Taro-Hayashi/KillerWhale/doc/leftside/4_TOP.md

# Killer Whale　TOP Unit LEFT Side Build Manual （[RIGHT Side](../rightside/4_TOP.md)）

1. [Start Page](../README_EN.md)
2. [BASE Unit](../leftside/2_BASE.md)
3. [SIDE Unit](../leftside/3_SIDE_TRACKBALL.md)
4. TOP Unit LEFT Side
   - [TOP Unit with wheel (sold separately)](../leftside/4_TOP_WHEEL.md)
5. [ADD Unit](../leftside/5_ADD.md)
6. [Assembly](../leftside/6_ASSEMBLE.md)
7. [Customizations](../leftside/7_CUSTOM.md)
8. [Misc](../leftside/8_MISC.md)
## Contents
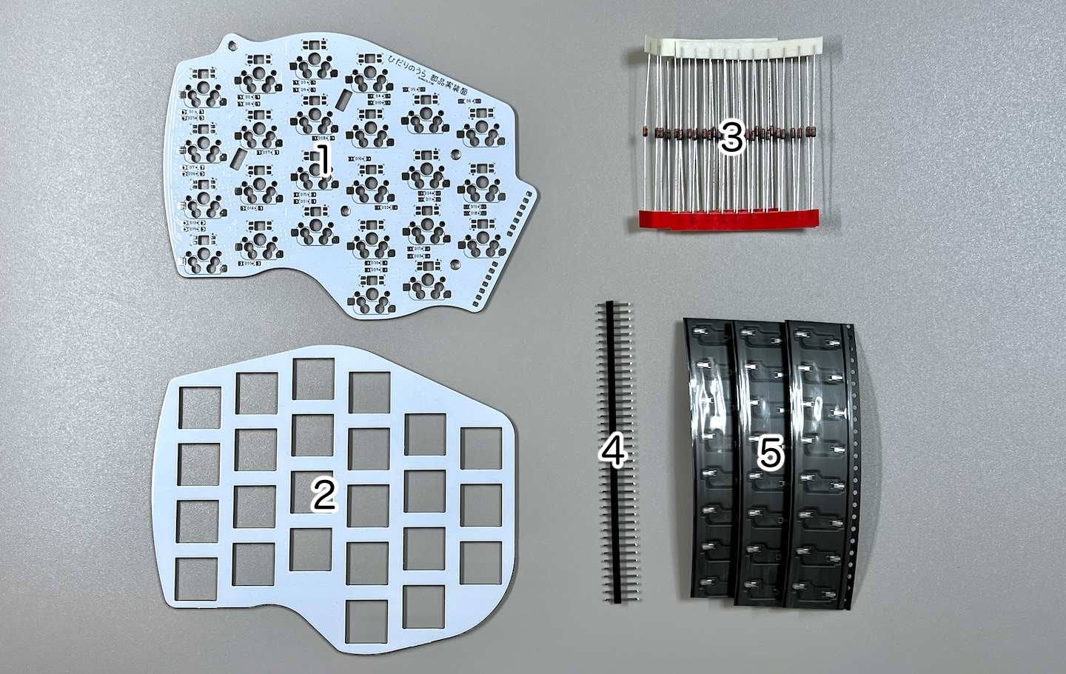
[picture p268: doc/img/4_1_top_l/4_1_1_contents.jpg]
  
||types|quantities||
|-|-|-|-|
|1|Main board|1|FR4|
|2|Switch plate|1|FR4|
|3|Diodes|30||
|4|Pin header|1||
|5|MX hotswap socket|24||

## Soldering

For the TOP unit, all components are soldered from the back side.
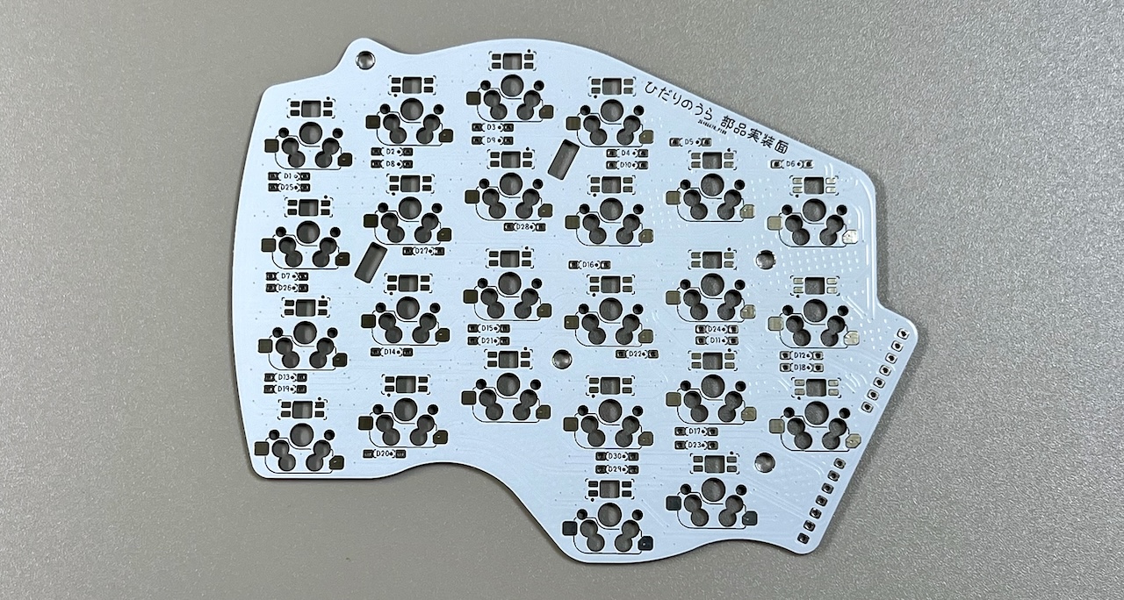
[picture p269: doc/img/4_1_top_l/4_1_2_overall.jpg]
  
### Soldering of the LEDs (optional)

> [!CAUTION]
> Orientation varies by location.

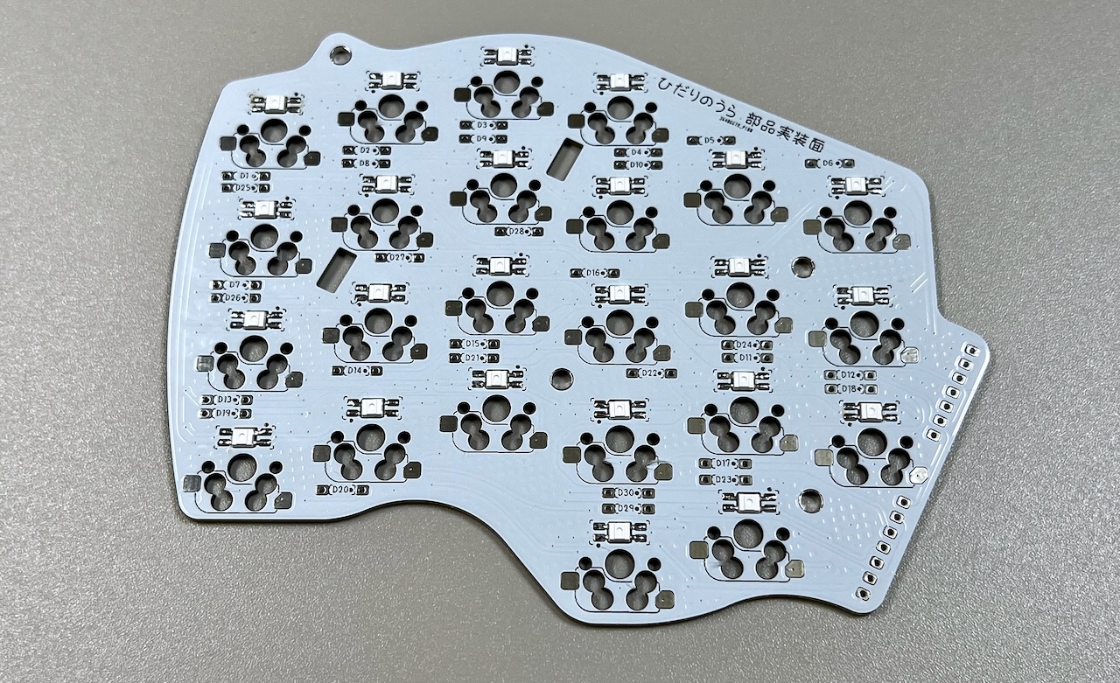
[picture p270: doc/img/4_1_top_l/4_1_3_led.jpg]
  

### Soldering of the diodes
Insert the diodes D1 to D30 from the bottom side of the PCB, and solder from the front side of the PCB and cut the diode legs.
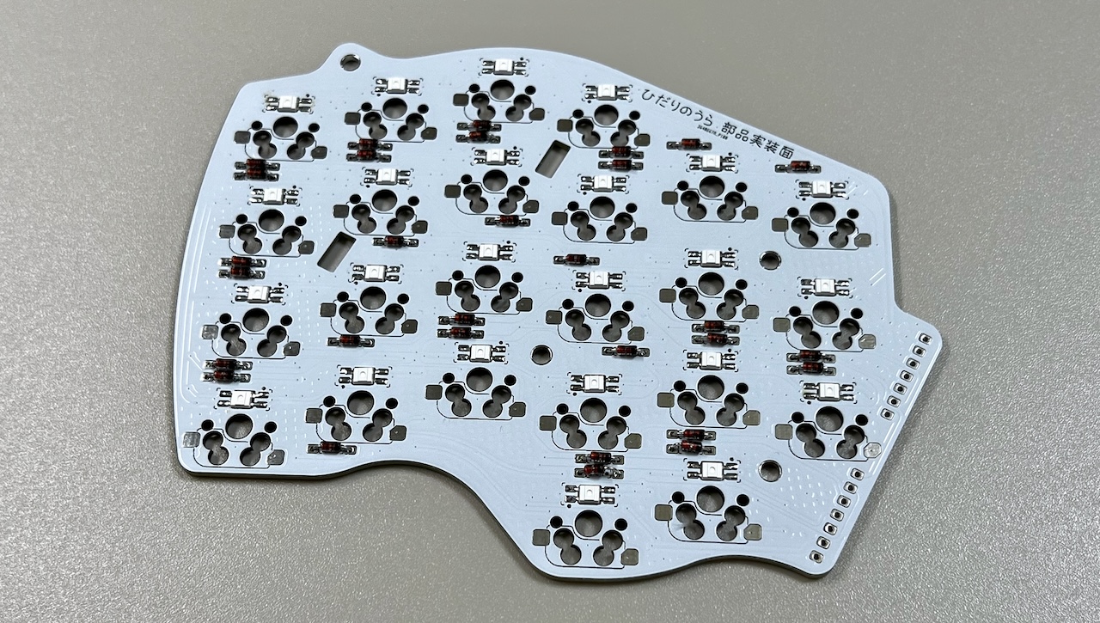
[picture p271: doc/img/4_1_top_l/4_1_4_diode.jpg]
 

### Soldering of the MX hotswap socket
Solder the MX hotswap sockets while keeping them in place with tweezers.
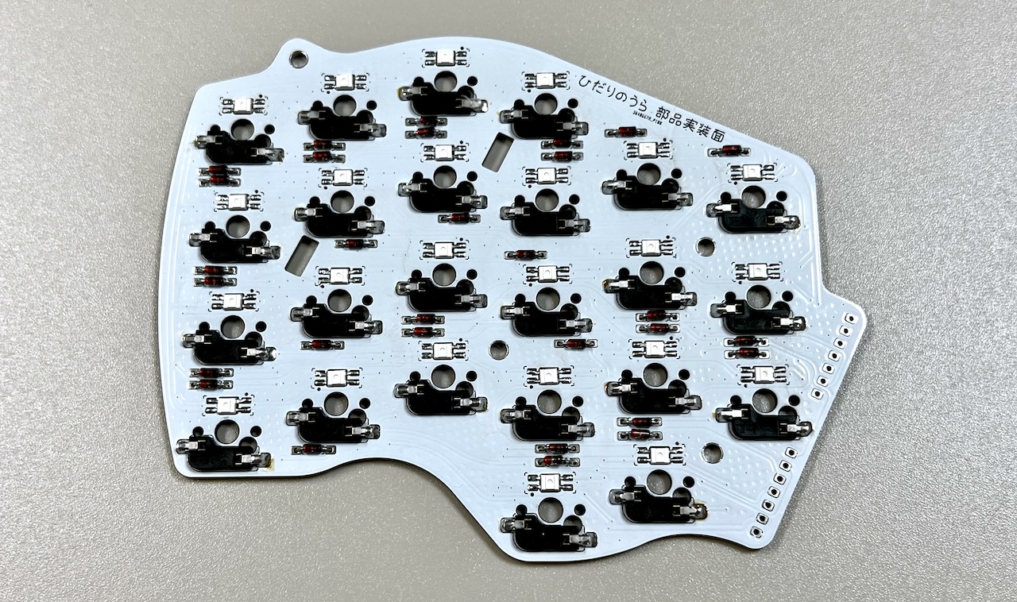
[picture p272: doc/img/4_1_top_l/4_1_5_mxsocket.jpg]
 

### Soldering od the pin headers
Cut out two sets of 7 pins from the 40 pin headers, insert from the back side of the PCB and solder. Insert the long side of the pins.
   
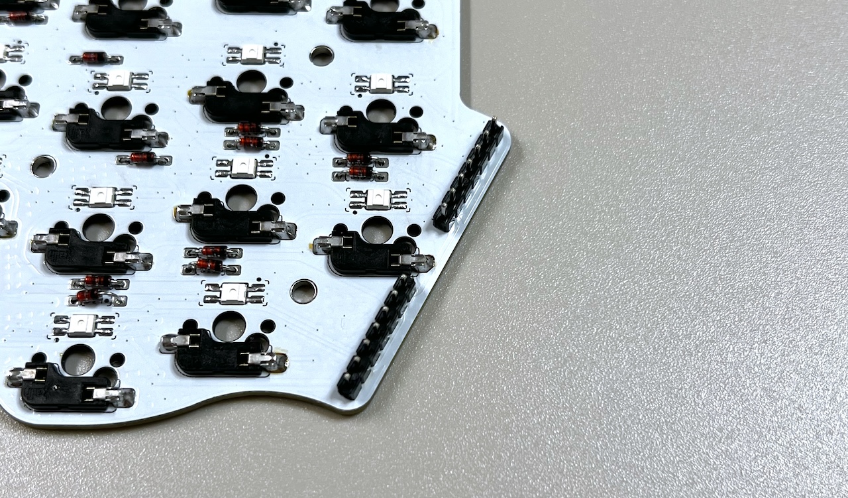
[picture p273: doc/img/4_1_top_l/4_1_6_pin_header.jpg]
 

## Intermediate assembly and soldering of sockets
If this is the first TOP unit that you have built, remove two sets of 7 pins from the remaining BASE unit pin headers, and insert them in the pin sockets of the TOP unit.

   
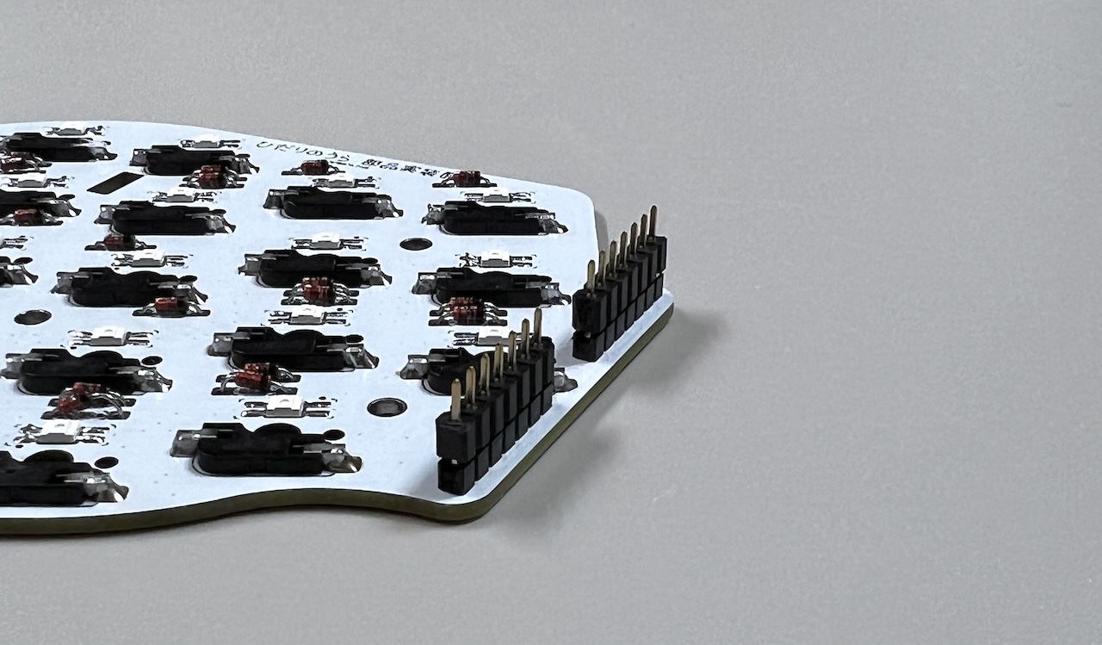
[picture p274: doc/img/4_1_top_l/4_1_7_pin_socket.jpg]
 
Place the TOP unit on the supports and secure it with the M3 screws excessed in base unit.
> [!NOTE]
>  Make sure that the legs of the pin sockets are inside the long through-holes of the base unit.

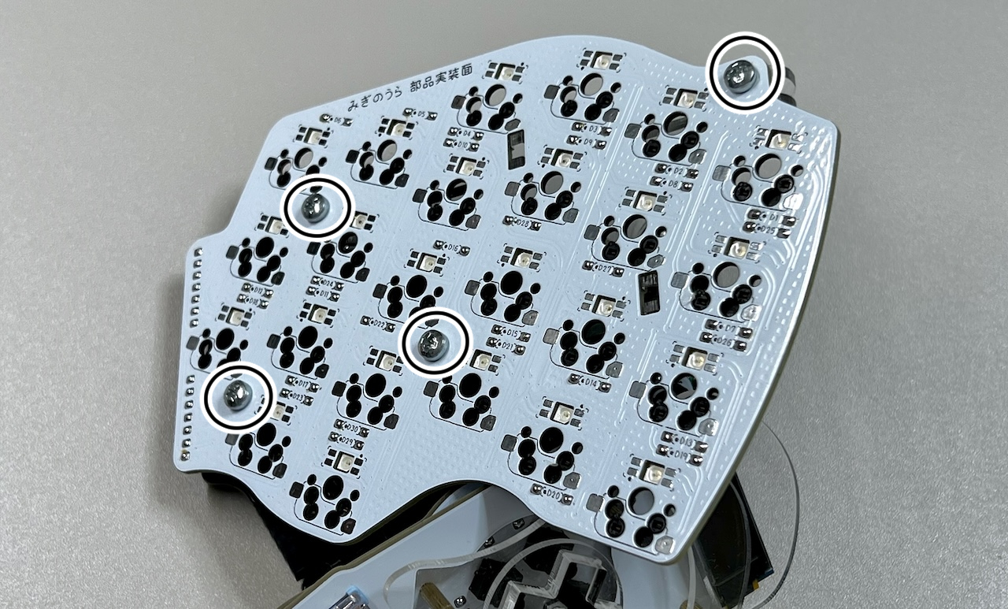
[picture p275: doc/img/4_1_top_l/4_1_8_base_1.jpg]
 
Solder the pin sockets from the back side of the base unit.
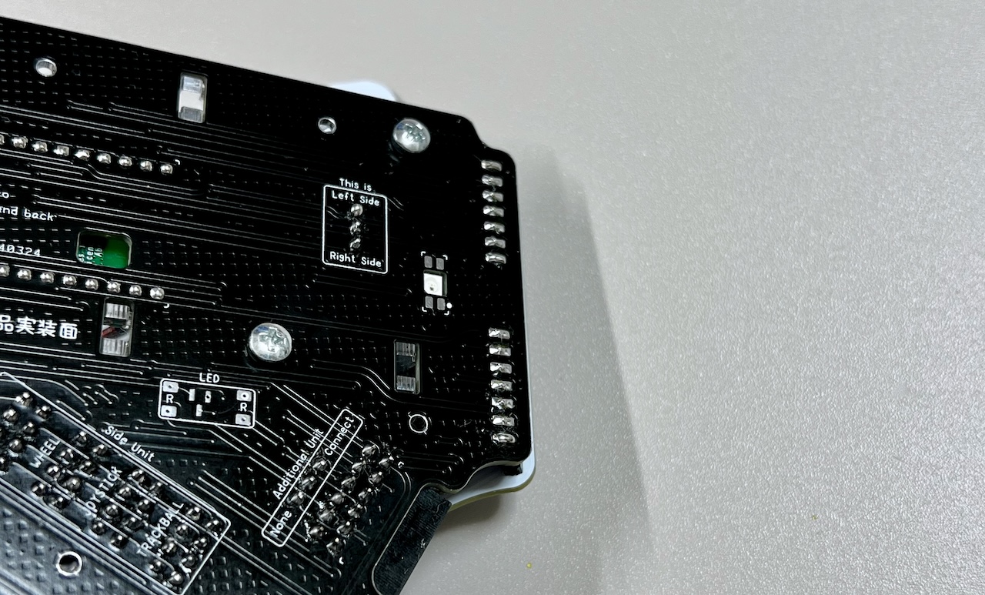
[picture p276: doc/img/4_1_top_l/4_1_9_base_2.jpg]
 
Switch plate and all switches are in place, then confirm that everything is working by connecting the unit to a computer with a USB cable. 
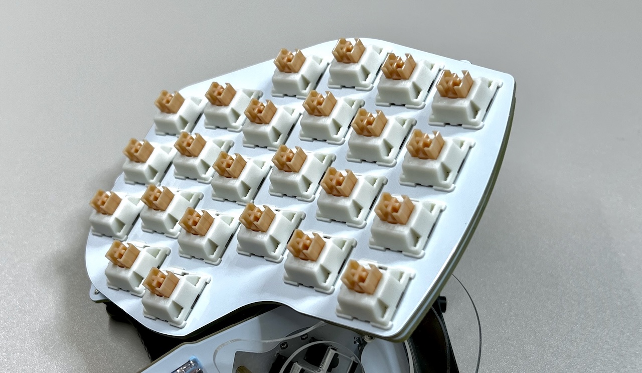
[picture p277: doc/img/4_1_top_l/4_1_10_base_complete.jpg]
  

The ADD unit is not mandatory. If you need it, proceed with the ADD unit build guide, otherwise proceed with the overall assembly guide

5. [ADD Unit](../leftside/5_ADD.md)
6. [Overall assembly](../leftside/6_ASSEMBLE.md)
