Taro-Hayashi/KillerWhale/doc/img/3_1_trackball_l/3_1_17_m2_screws.jpg

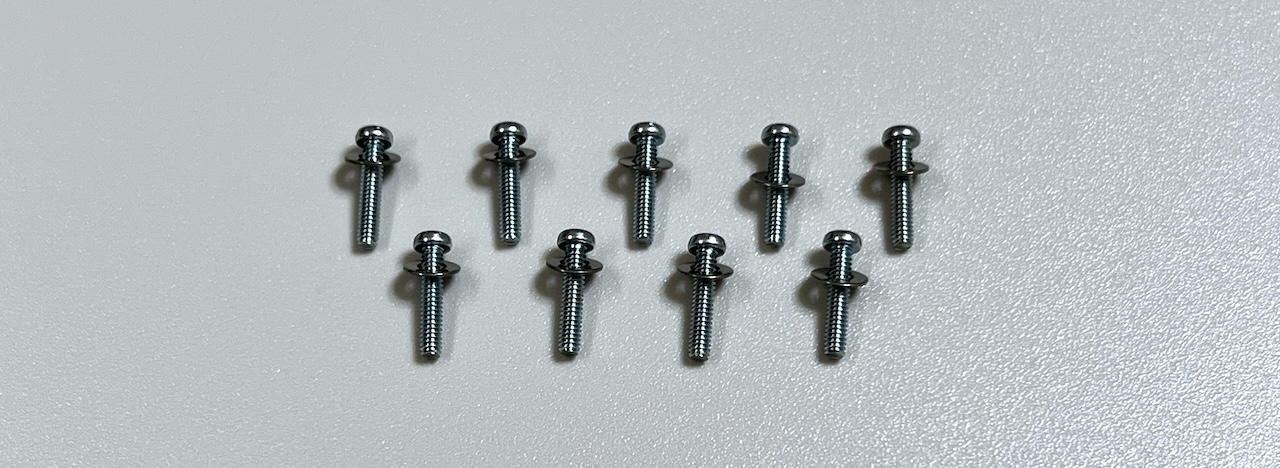
doc/img/3_1_trackball_l/3_1_17_m2_screws.jpg
