Taro-Hayashi/KillerWhale/doc/img/3_1_trackball_l/3_1_20_pillars_3.jpg

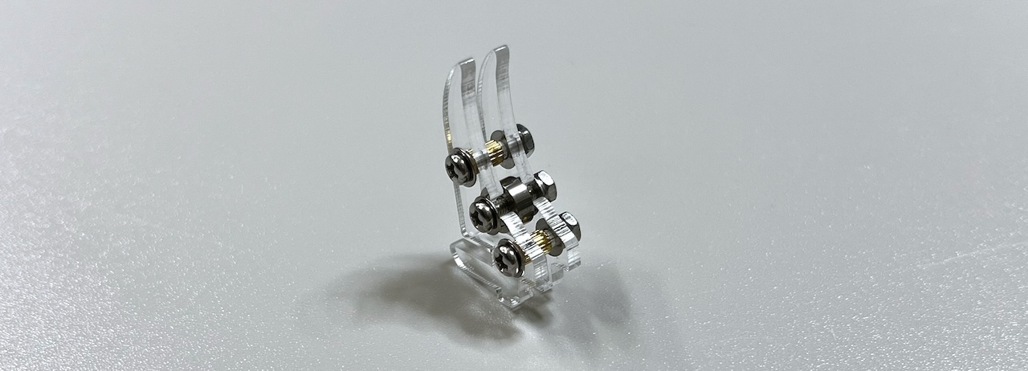
doc/img/3_1_trackball_l/3_1_20_pillars_3.jpg
