Taro-Hayashi/KillerWhale/doc/img/3_1_trackball_l/3_1_21_pillars_4.jpg

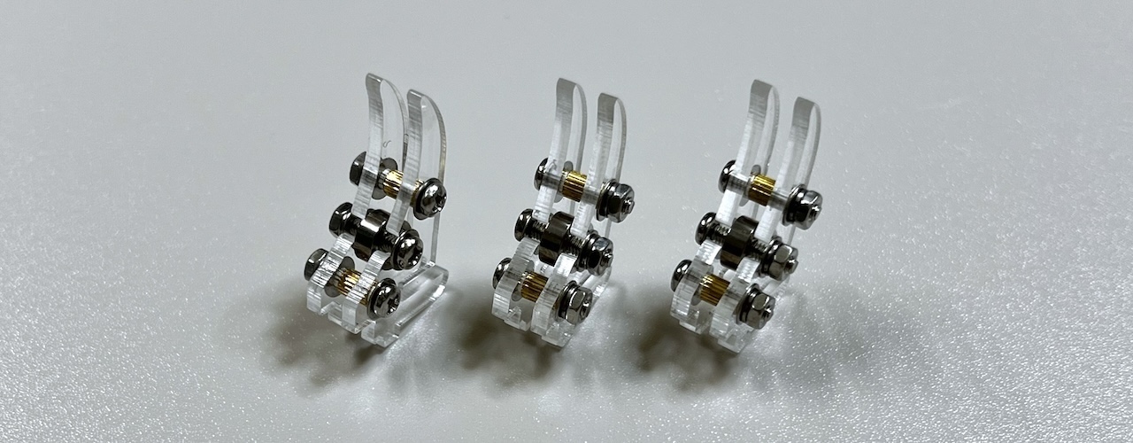
doc/img/3_1_trackball_l/3_1_21_pillars_4.jpg
