Taro-Hayashi/KillerWhale/doc/img/3_1_trackball_l/3_1_22_m3_screws.jpg

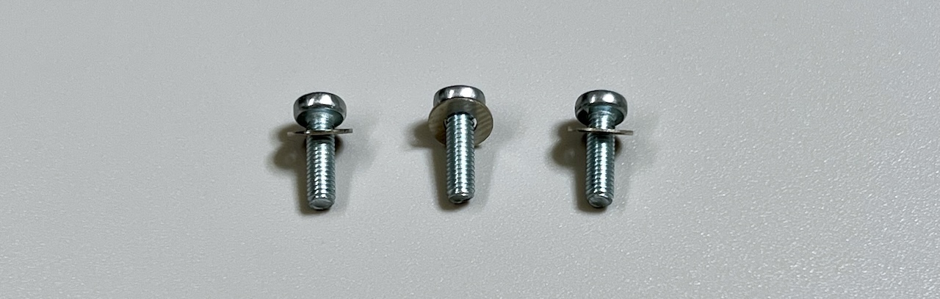
doc/img/3_1_trackball_l/3_1_22_m3_screws.jpg
