Taro-Hayashi/KillerWhale/doc/img/3_1_trackball_l/3_1_25_pillars_complete.jpg

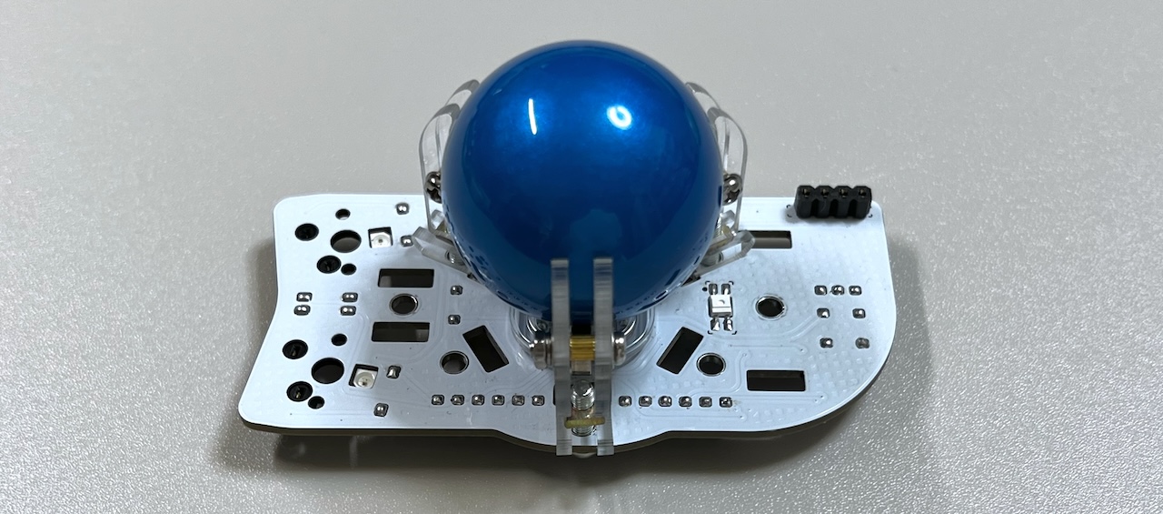
doc/img/3_1_trackball_l/3_1_25_pillars_complete.jpg
