Taro-Hayashi/KillerWhale/doc/img/3_1_trackball_r/3_1_30_complete.jpg

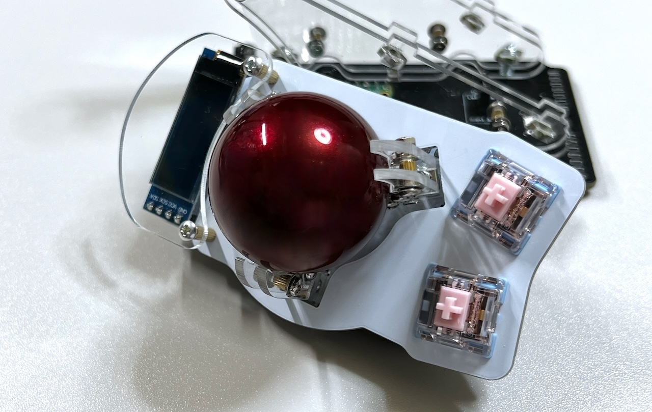
doc/img/3_1_trackball_r/3_1_30_complete.jpg
