Taro-Hayashi/KillerWhale/doc/img/3_2_dpad_r/3_1_30_dpad.jpg

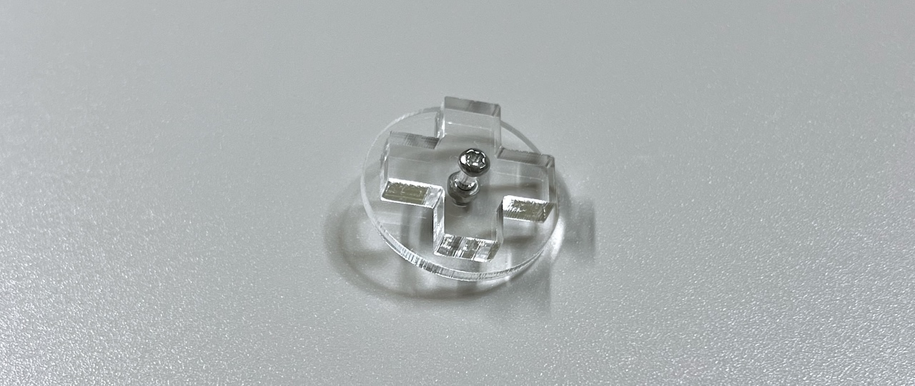
doc/img/3_2_dpad_r/3_1_30_dpad.jpg
