Taro-Hayashi/KillerWhale/doc/img/custom/any.png

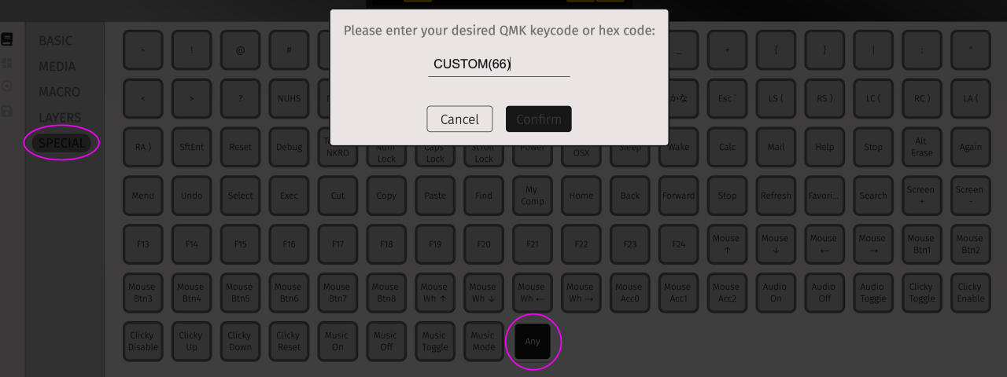
doc/img/custom/any.png
