Taro-Hayashi/KillerWhale/doc/img/custom/auto_e.png

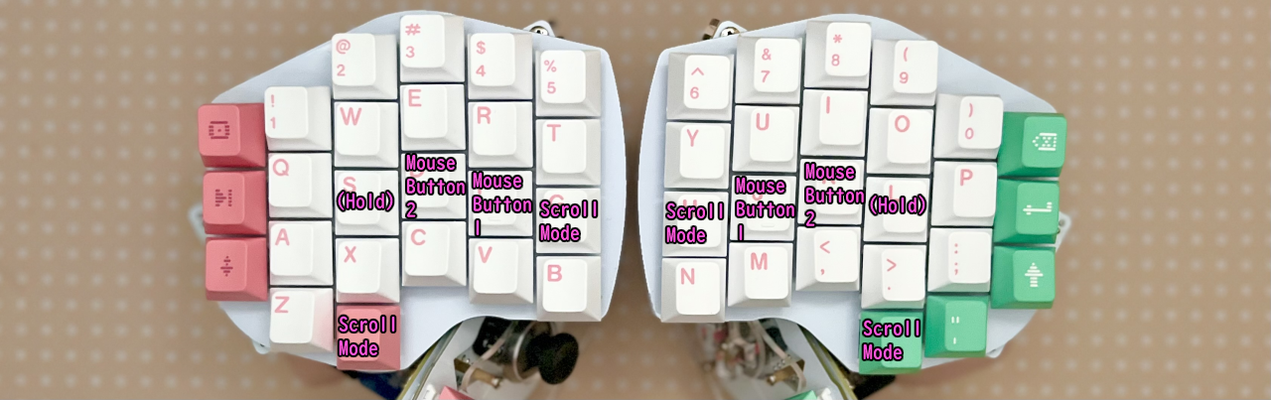
doc/img/custom/auto_e.png
