Taro-Hayashi/KillerWhale/doc/img/custom/click.jpg

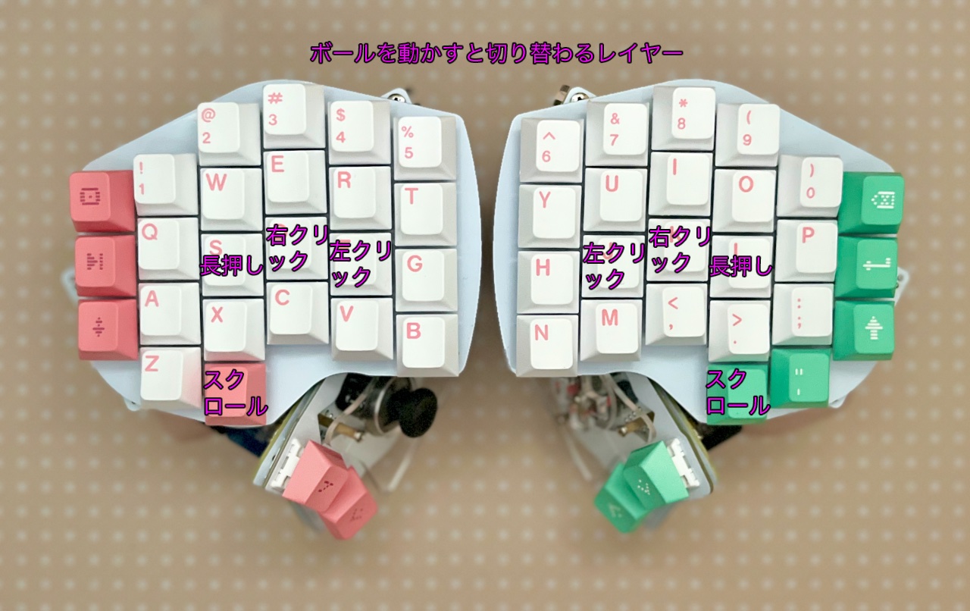
doc/img/custom/click.jpg
