Taro-Hayashi/KillerWhale/doc/img/custom/IMG_5884.jpg

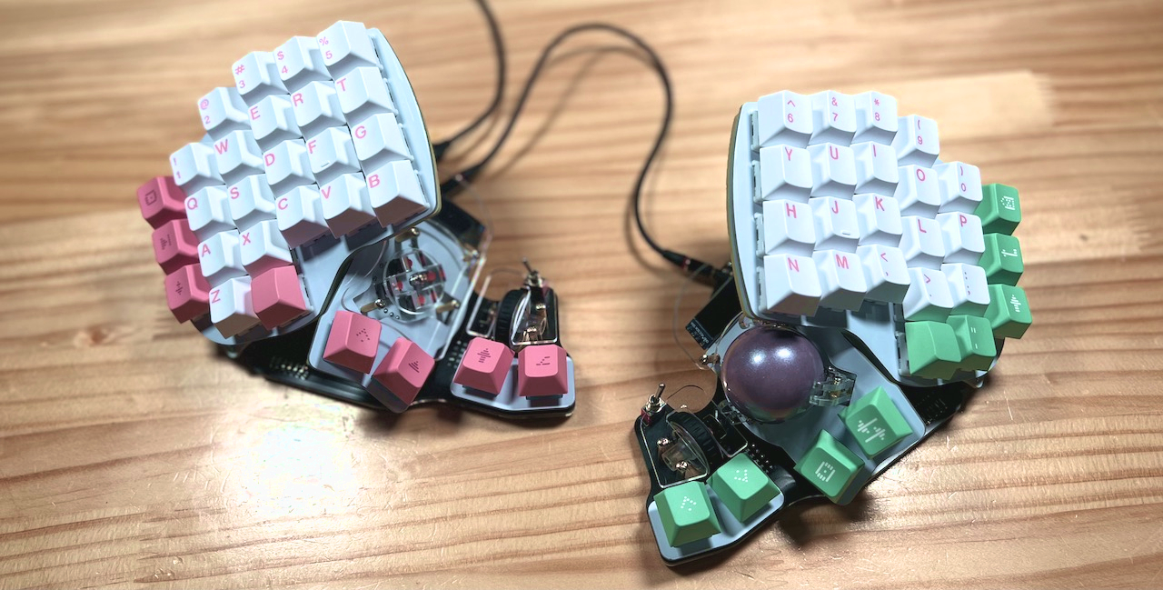
doc/img/custom/IMG_5884.jpg
