Taro-Hayashi/KillerWhale/doc/img/custom/led_e.png

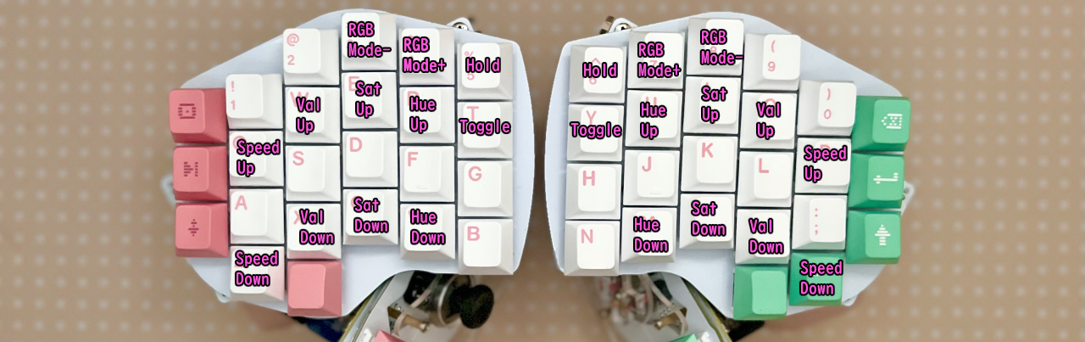
doc/img/custom/led_e.png
