Taro-Hayashi/KillerWhale/doc/img/custom/mouse.png

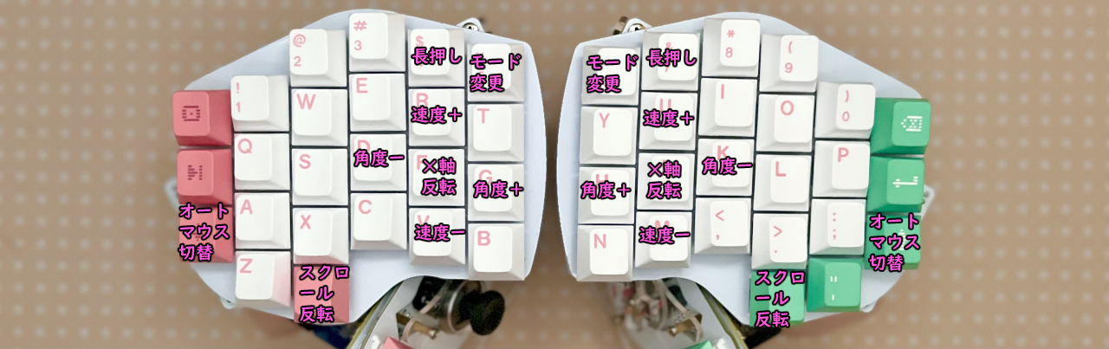
doc/img/custom/mouse.png
