Taro-Hayashi/KillerWhale/doc/img/custom/rgb_j.jpg

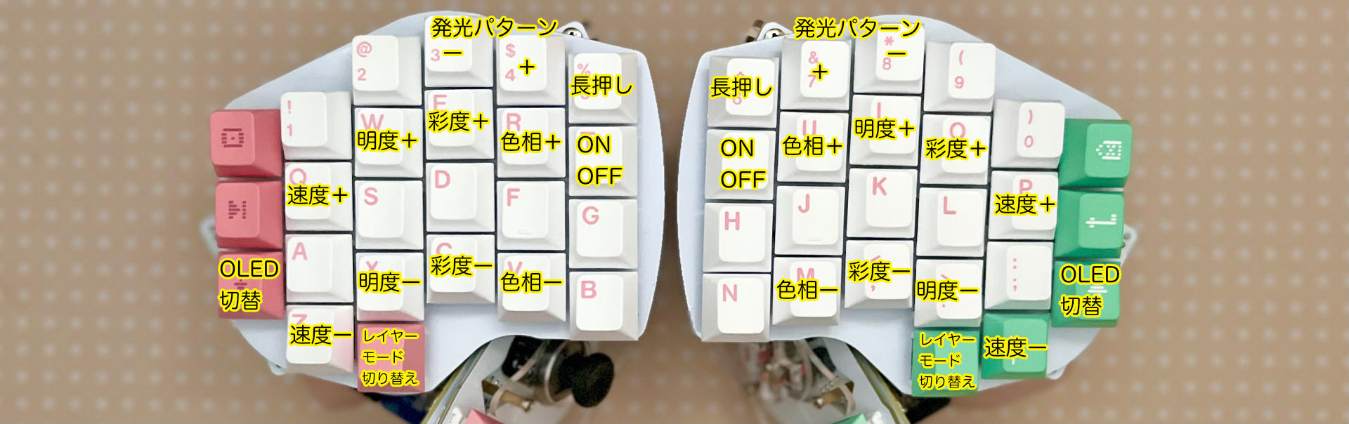
doc/img/custom/rgb_j.jpg
