Taro-Hayashi/KillerWhale/doc/img/custom/via1.png

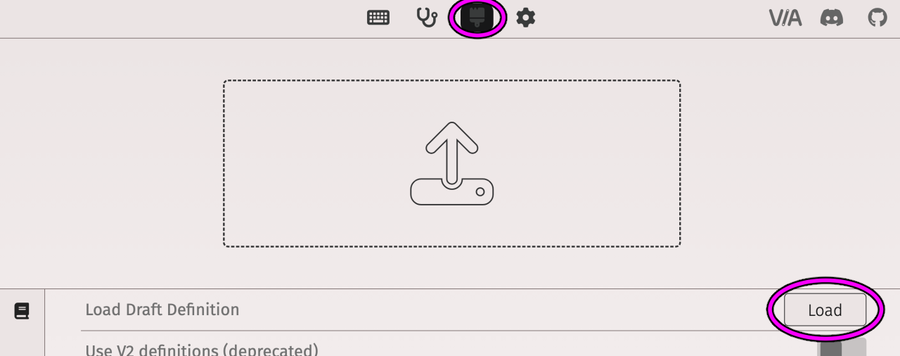
doc/img/custom/via1.png
