Taro-Hayashi/KillerWhale/doc/img/pending/IMG_0490.jpeg

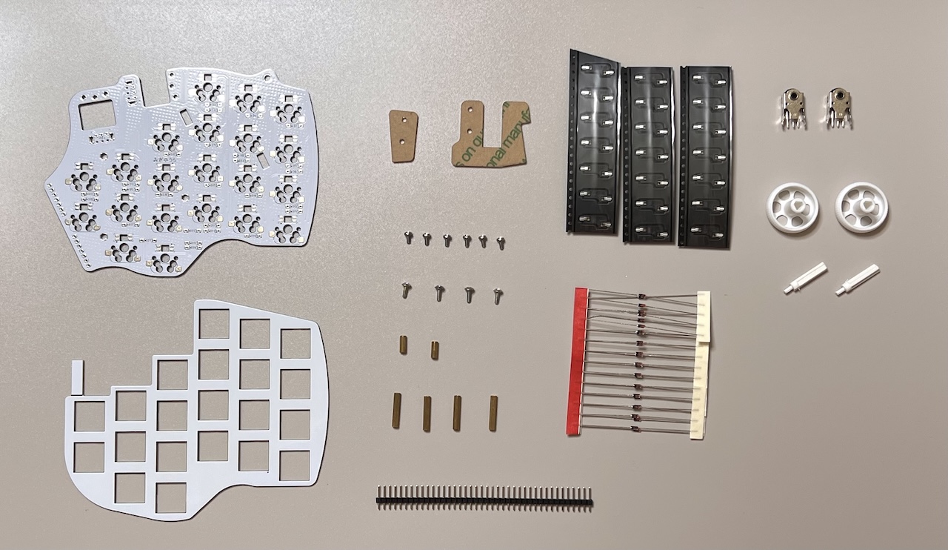
doc/img/pending/IMG_0490.jpeg
