Taro-Hayashi/KillerWhale/doc/img/pending/IMG_0517.jpeg

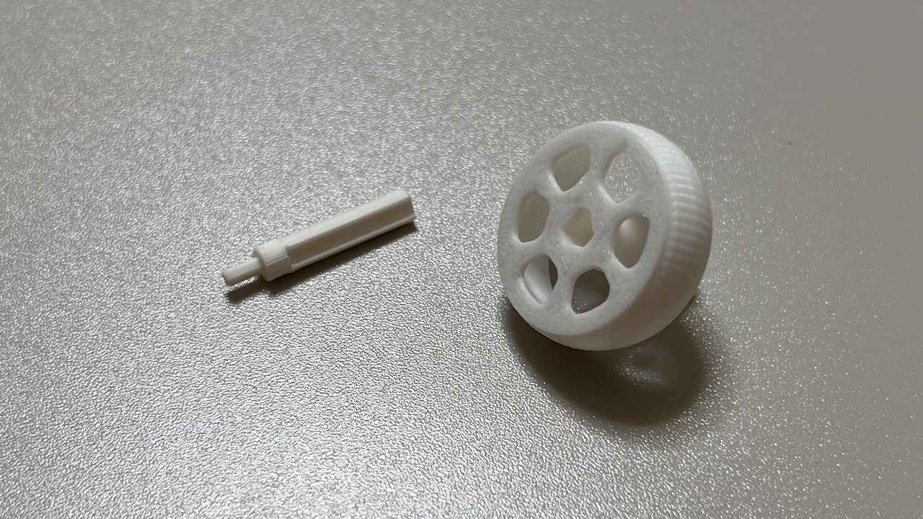
doc/img/pending/IMG_0517.jpeg
