Taro-Hayashi/KillerWhale/img/3DP/4_1_Wheel.jpeg

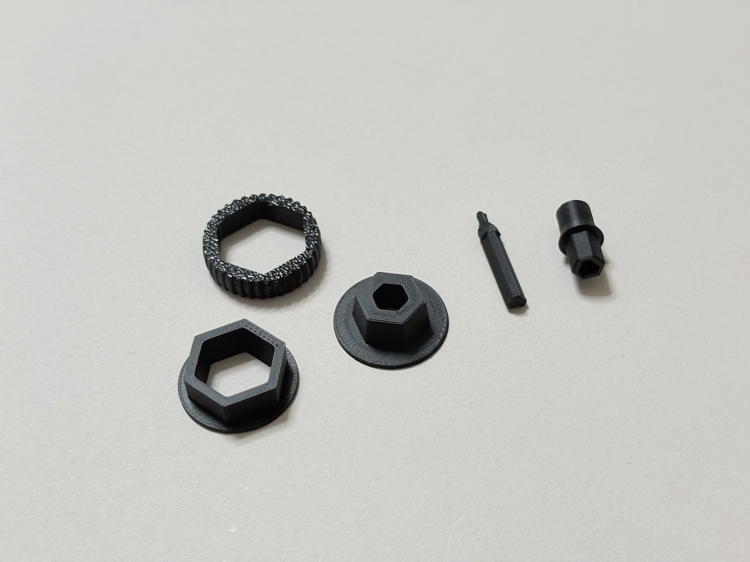
img/3DP/4_1_Wheel.jpeg
