Taro-Hayashi/KillerWhale/img/start/IMG_4615.jpeg

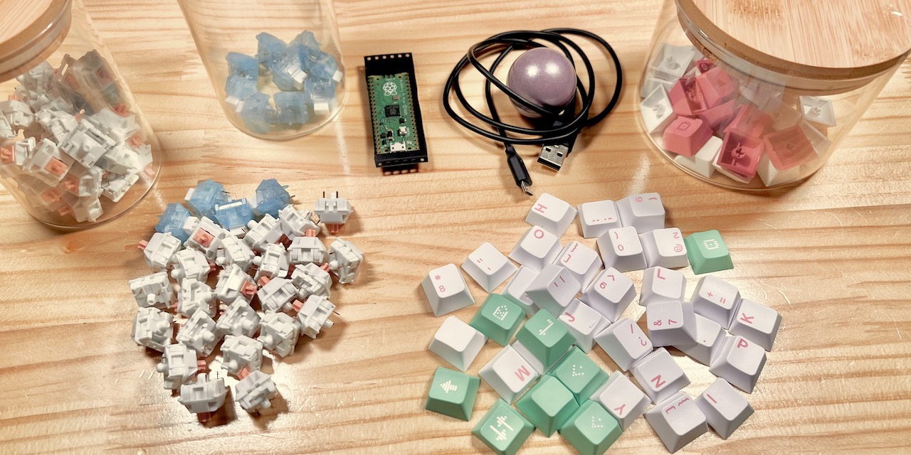
img/start/IMG_4615.jpeg
