Taro-Hayashi/KillerWhale/img/start/IMG_4630.jpeg

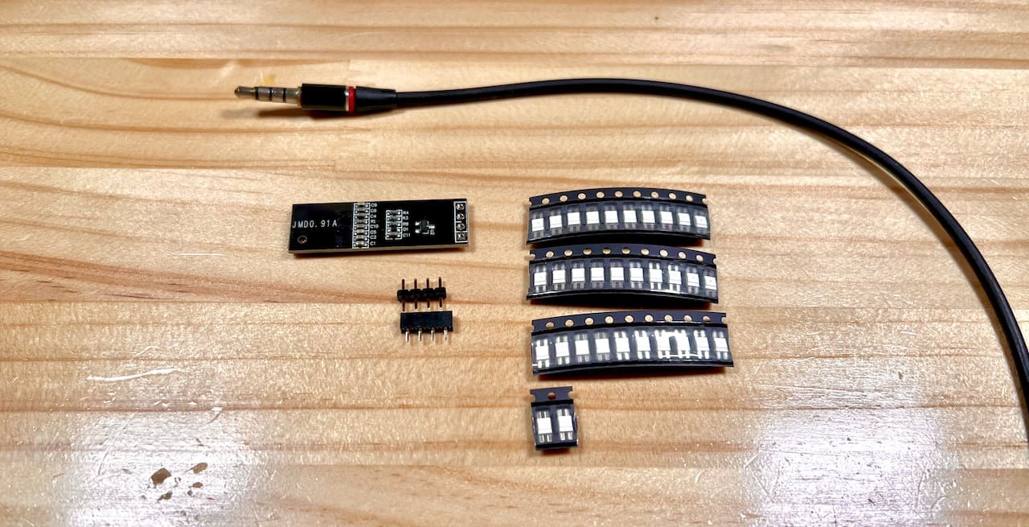
img/start/IMG_4630.jpeg
