Taro-Hayashi/KillerWhale/img/start/IMG_4649.jpeg

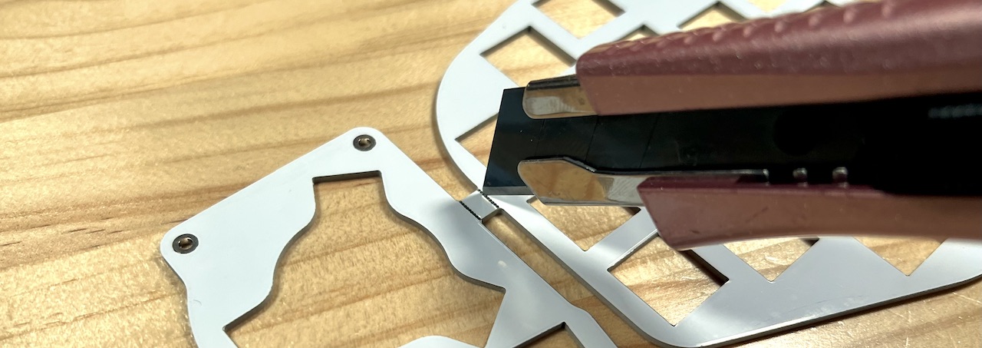
img/start/IMG_4649.jpeg
