Taro-Hayashi/KillerWhale/stl/Wheel/Ring.stl

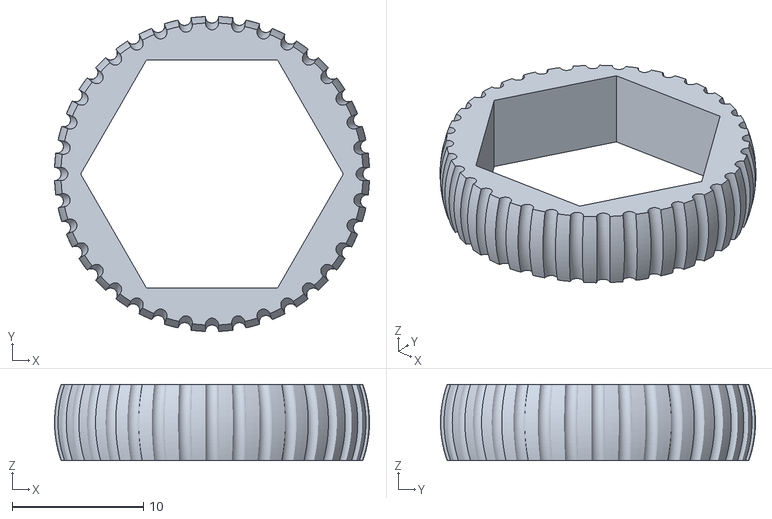
[picture p352: CAD file, 2025-05-16]
stl/Wheel/Ring.stl
24.0 x 24.0 x 5.80
