Taro-Hayashi/KillerWhale/stl/Sphere_Unit/0.2mm.stl

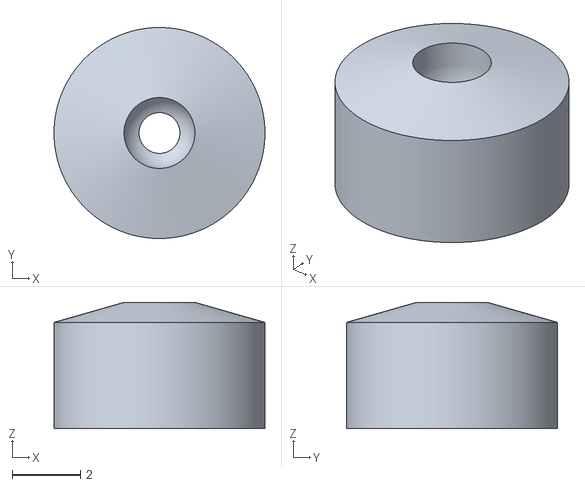
[picture p353: CAD file, 2025-01-16]
stl/Sphere_Unit/0.2mm.stl
6.20 x 6.20 x 3.71
