Taro-Hayashi/KillerWhale/stl/Wheel/Wheel2.stl

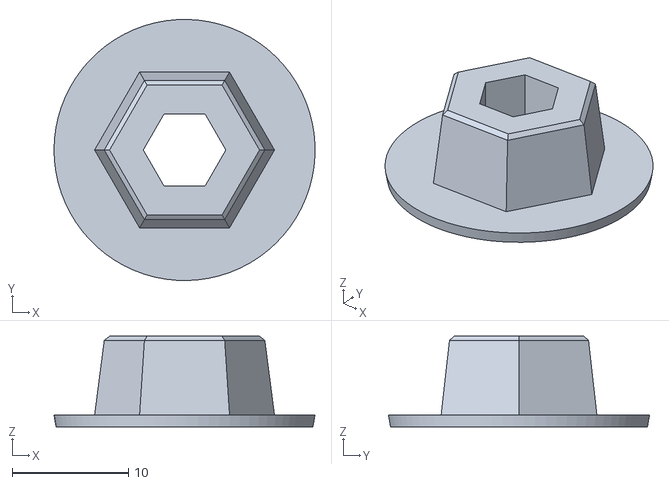
[picture p354: CAD file, 2025-05-16]
stl/Wheel/Wheel2.stl
22.5 x 22.5 x 7.80
